juusolonen/juubo/v2/case/case_left.stl

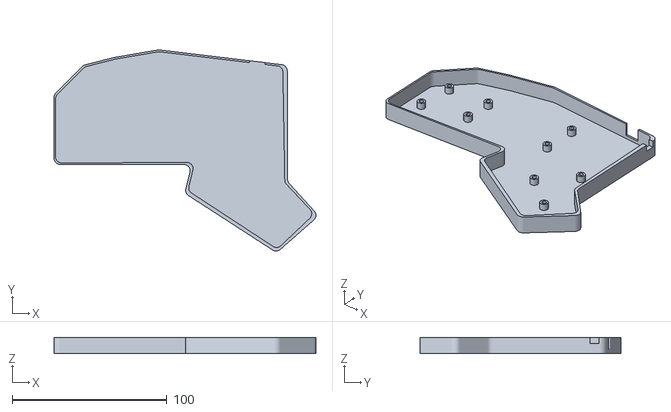
[picture p17: CAD file, 2026-02-04]
v2/case/case_left.stl
169.4 x 130.1 x 10.6
