juusolonen/juubo/ergogen/output/outlines/xlBoard.dxf

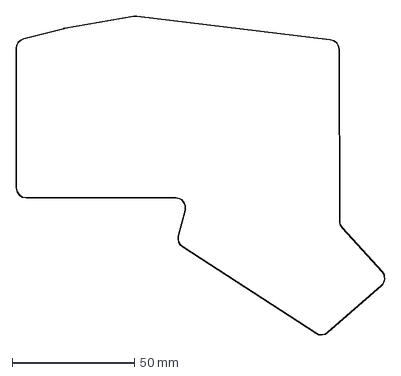
[picture p18: CAD file, 2024-03-10]
ergogen/output/outlines/xlBoard.dxf
150.5 x 130.5 mm
