juusolonen/juubo/external-3d-models/DSA 1.5.stl

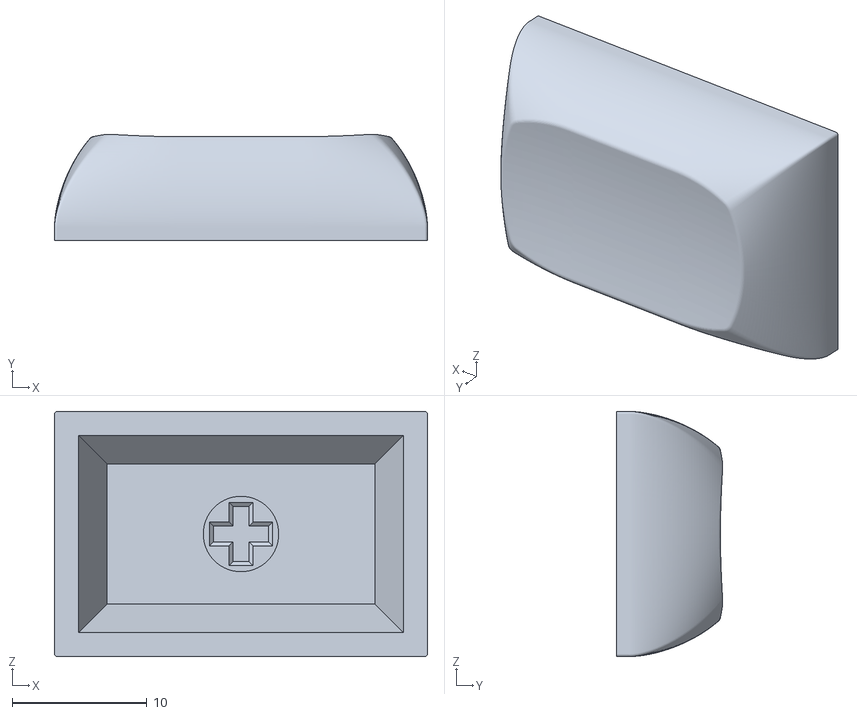
[picture p19: CAD file, 2024-02-23]
external-3d-models/DSA 1.5.stl
27.7 x 7.91 x 18.2
