juusolonen/juubo/ergogen/output/cases/switchPlateWithStandLeft.stl

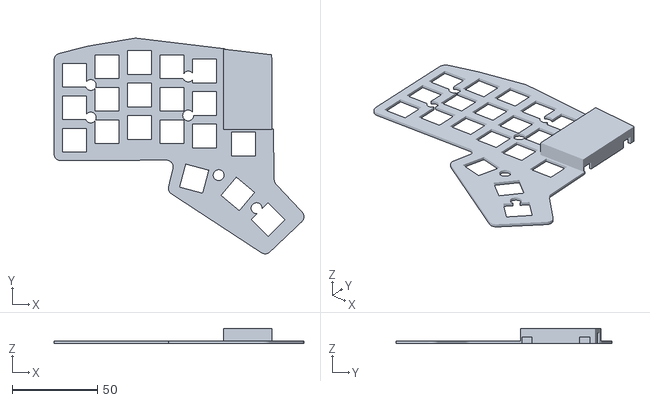
[picture p20: CAD file, 2024-03-10]
ergogen/output/cases/switchPlateWithStandLeft.stl
146.7 x 126.6 x 9.00
