juusolonen/juubo/ergogen/output/outlines/xlBoardRight.dxf

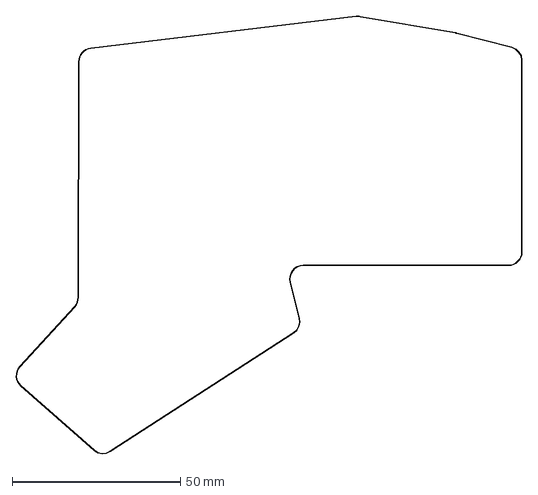
[picture p21: CAD file, 2024-03-10]
ergogen/output/outlines/xlBoardRight.dxf
150.5 x 130.5 mm
