juusolonen/juubo/ergogen/output/outlines/raw.dxf

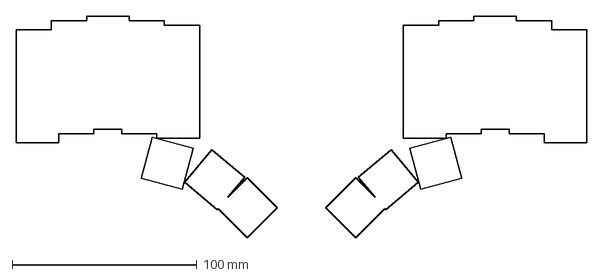
[picture p22: CAD file, 2024-01-21]
ergogen/output/outlines/raw.dxf
308.8 x 120.0 mm
