juusolonen/juubo/ergogen/output/cases/xlBottomRight.stl

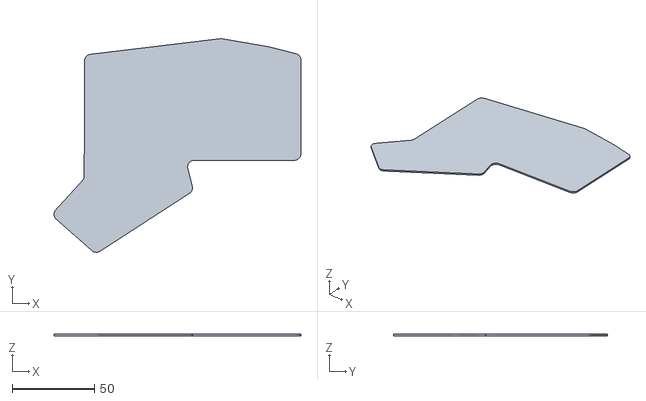
[picture p23: CAD file, 2024-03-10]
ergogen/output/cases/xlBottomRight.stl
150.4 x 130.1 x 1.00
