juusolonen/juubo/ergogen/output/outlines/keys.dxf

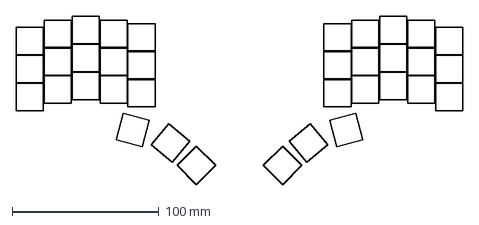
[picture p24: CAD file, 2024-01-21]
ergogen/output/outlines/keys.dxf
304.3 x 114.6 mm
