juusolonen/juubo/ergogen/output/outlines/switches.dxf

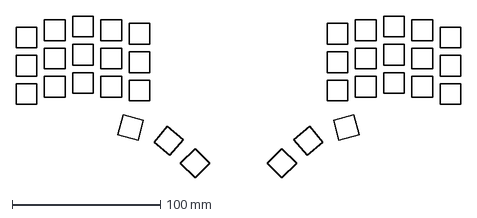
[picture p25: CAD file, 2024-01-21]
ergogen/output/outlines/switches.dxf
299.8 x 109.1 mm
