juusolonen/juubo/ergogen/output/outlines/extraArea.dxf

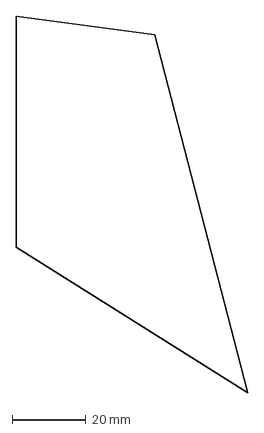
[picture p26: CAD file, 2024-01-21]
ergogen/output/outlines/extraArea.dxf
62.7 x 102.2 mm
