juusolonen/juubo/ergogen/output/cases/stand.stl

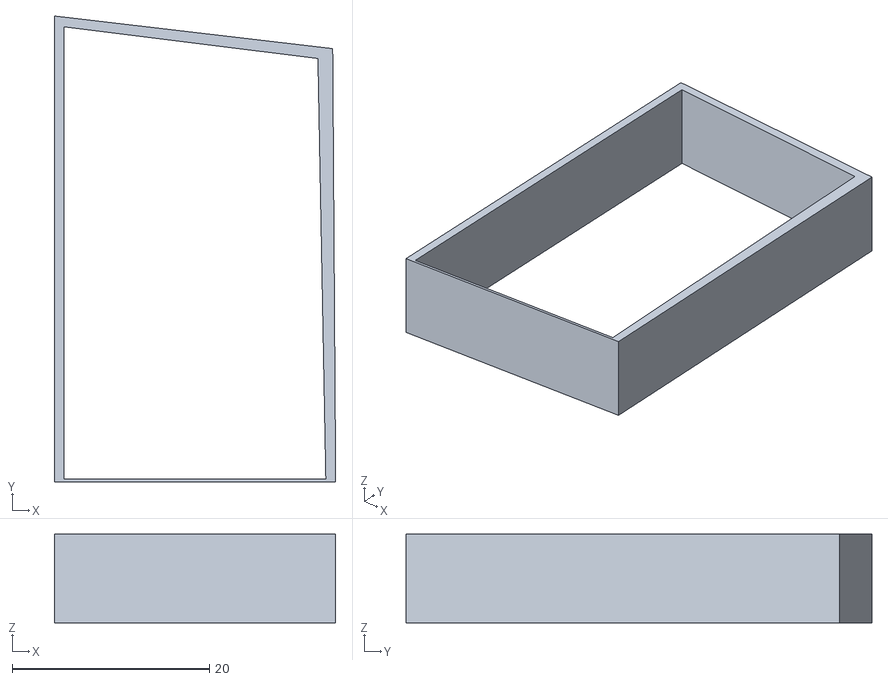
[picture p27: CAD file, 2024-03-10]
ergogen/output/cases/stand.stl
28.5 x 47.2 x 9.00
