juusolonen/juubo/ergogen/output/outlines/finalMount.dxf

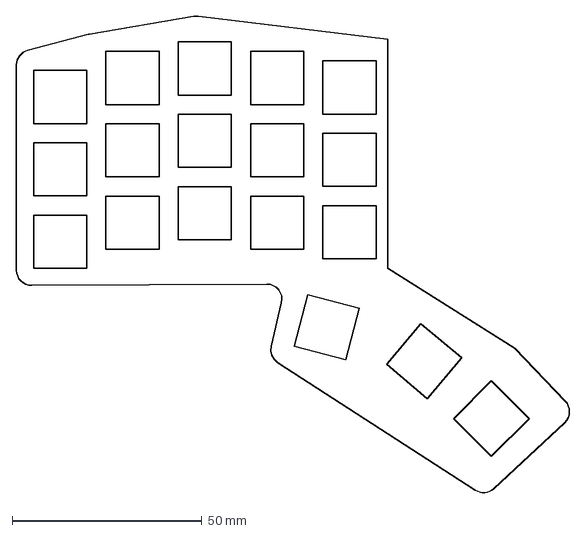
[picture p28: CAD file, 2024-01-21]
ergogen/output/outlines/finalMount.dxf
145.7 x 125.9 mm
