juusolonen/juubo/ergogen/output/cases/switchPlate.stl

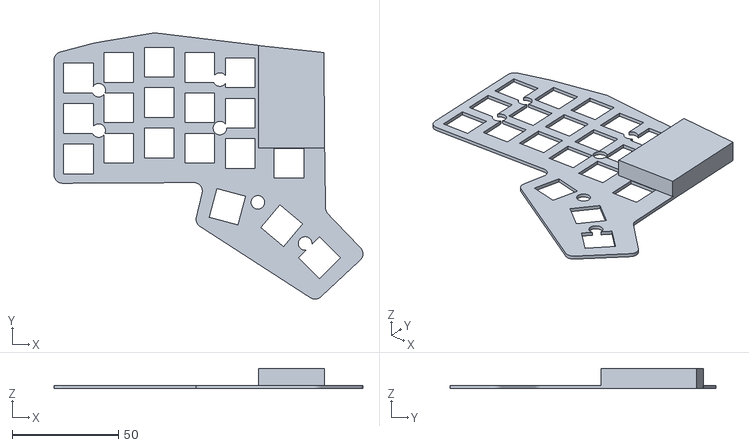
[picture p29: CAD file, 2024-02-12]
ergogen/output/cases/switchPlate.stl
145.6 x 125.5 x 9.60
