juusolonen/juubo/ergogen/output/outlines/mounting.dxf

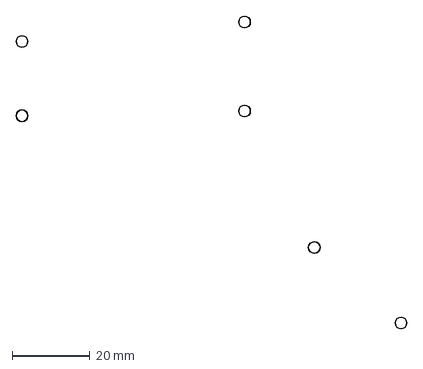
[picture p30: CAD file, 2024-01-19]
ergogen/output/outlines/mounting.dxf
100.3 x 80.2 mm
