juusolonen/juubo/ergogen/output/outlines/standoff.dxf

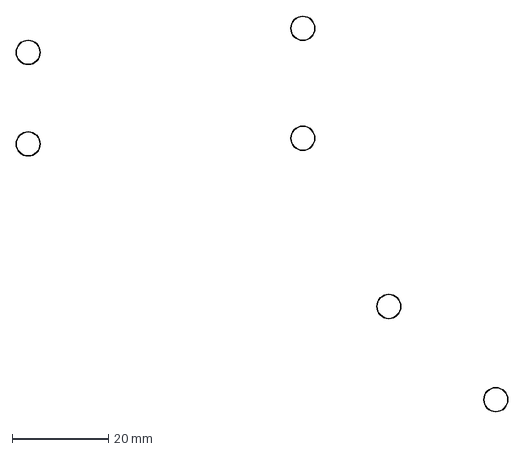
[picture p31: CAD file, 2024-01-19]
ergogen/output/outlines/standoff.dxf
102.3 x 82.2 mm
