juusolonen/juubo/ergogen/output/outlines/board.dxf

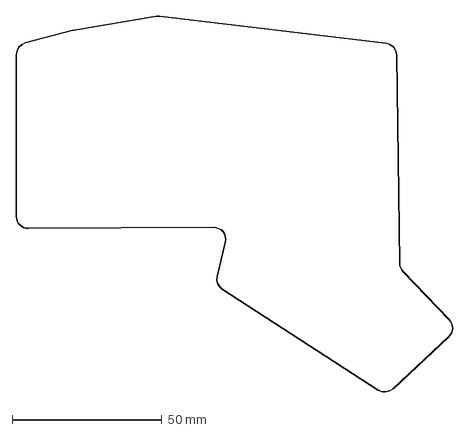
[picture p32: CAD file, 2024-01-14]
ergogen/output/outlines/board.dxf
145.7 x 125.9 mm
